1917570484cz-source/sensor-final-project/data/calibration/heading_residual_cv_20260705_170052.csv

phase | source | reference | measured | raw_error | correction | corrected | corrected_error
train | data\heading_12dir_20260705_151120.csv | 0.0 | 98.19598547600593 | 98.19598547600594 | -94.11017907317277 | 4.085806402833157 | 4.085806402833157
train | data\heading_12dir_20260705_151120.csv | 30.0 | 127.44926723604284 | 97.44926723604283 | -93.15444189108254 | 34.2948253449603 | 4.294825344960316
train | data\heading_12dir_20260705_151120.csv | 60.0 | 154.43828876907028 | 94.43828876907025 | -94.42048358766432 | 60.01780518140596 | 0.017805181405947224
train | data\heading_12dir_20260705_151120.csv | 90.0 | 187.5472009397793 | 97.54720093977926 | -95.92516730034265 | 91.62203363943664 | 1.622033639436637
train | data\heading_12dir_20260705_151120.csv | 120.0 | 222.07453650956208 | 102.07453650956211 | -93.25203372734123 | 128.82250278222085 | 8.822502782220852
train | data\heading_12dir_20260705_151120.csv | 150.0 | 245.8710865356573 | 95.8710865356573 | -92.37840262034192 | 153.49268391531538 | 3.492683915315382
train | data\heading_12dir_20260705_151120.csv | 180.0 | 254.01499349429668 | 74.01499349429668 | -93.06132880562059 | 160.9536646886761 | -19.0463353113239
train | data\heading_12dir_20260705_151120.csv | 210.0 | 321.9503647090293 | 111.95036470902932 | -108.02195298728873 | 213.9284117217406 | 3.928411721740588
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
valid | data\heading_12dir_20260705_162311_best_re300_165648.csv | 300.0 | 43.52006637195349 | 103.52006637195348 | -96.5805253654883 | 306.9395410064652 | 6.93954100646522
valid | data\heading_12dir_20260705_162311_best_re300_165648.csv | 330.0 | 64.96421444106312 | 94.96421444106312 | -95.56517152211771 | 329.3990429189454 | -0.6009570810546165
