1917570484cz-source/sensor-final-project/data/calibration/heading_12dir_20260705_162311_best_re300_165648.csv

reference_deg | yaw_flat_deg | yaw_flat_err_deg | yaw_tilt_deg | yaw_tilt_err_deg | mahony_yaw_deg | mahony_yaw_err_deg | roll_deg | pitch_deg | rows | yaw_flat_offset_deg | yaw_flat_offset_err_deg | yaw_tilt_offset_deg | yaw_tilt_offset_err_deg | mahony_offset_deg | mahony_offset_err_deg
0.0 | 95.1120477197996 | 95.11204771979959 | 93.50833330320133 | 93.50833330320131 | 89.66409134850906 | 89.66409134850903 | 9.359337531486146 | 1.5659093198992444 | 397 | 1.4210854715202004e-14 | 0.0 | 1.4210854715202004e-14 | 0.0 | 2.842170943040401e-14 | 2.842170943040401e-14
30.0 | 122.40377727304802 | 92.40377727304804 | 119.45609862145093 | 89.4560986214509 | 119.34203227396702 | 89.34203227396699 | 4.141942028985507 | 3.763937198067633 | 414 | 25.540948633397576 | -4.459051366602409 | 22.058626675852466 | -7.941373324147548 | 27.3919015030843 | -2.6080984969157157
60.0 | 154.37254968711343 | 94.3725496871134 | 150.82194170462606 | 90.82194170462606 | 146.95494871060683 | 86.9549487106068 | 4.423045 | 4.42563 | 400 | 60.00000000000003 | 2.842170943040401e-14 | 60.0 | 0.0 | 60.00000000000003 | 2.842170943040401e-14
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
