1917570484cz-source/sensor-final-project/data/calibration/mag_rotate_20260705_135521.csv

t_s | ax_raw_g | ay_raw_g | az_raw_g | gx_raw_dps | gy_raw_dps | gz_raw_dps | ax_g | ay_g | az_g | gx_dps | gy_dps | gz_dps | mpu_temp_c | roll_deg | pitch_deg | bx_uT | by_uT | bz_uT | mag_uT | bx_cal_uT | by_cal_uT | bz_cal_uT | mag_cal_uT | yaw_flat_deg | yaw_tilt_deg | mahony_roll_deg | mahony_pitch_deg | mahony_yaw_deg | bmp_temp_c | pressure_pa | altitude_m
495.637 | 0.05957 | 0.339111 | -1.015869 | -3.022901 | 2.778626 | -2.854962 | 0.08092 | 0.36251 | -0.958087 | -4.472157 | 3.623879 | -3.427169 | 43.477 | 163.705 | 6.041 | -16.9725 | -38.3486 | -21.6514 | 47.196 | -17.9444 | -78.3829 | -81.5728 | 114.5426 | 102.895 | 263.074 | 159.804 | -2.553 | 259.868 | 26.86 | 100572.35 | -139.935
495.747 | 0.045654 | 0.381836 | -1.022461 | -25.465649 | 1.007634 | -10.793893 | 0.068197 | 0.405787 | -0.964131 | -26.914387 | 1.853557 | -11.366401 | 43.486 | 160.673 | 6.045 | -17.5229 | -38.4404 | -21.2844 | 47.3048 | -18.5292 | -78.4503 | -81.2075 | 114.4223 | 103.289 | 262.608 | 156.491 | -2.353 | 260.996 | 26.86 | 100571.68 | -139.877
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
